ImperialCollegeLondon/Interface-Matters/gumi/base/stl/BaseTop.stl

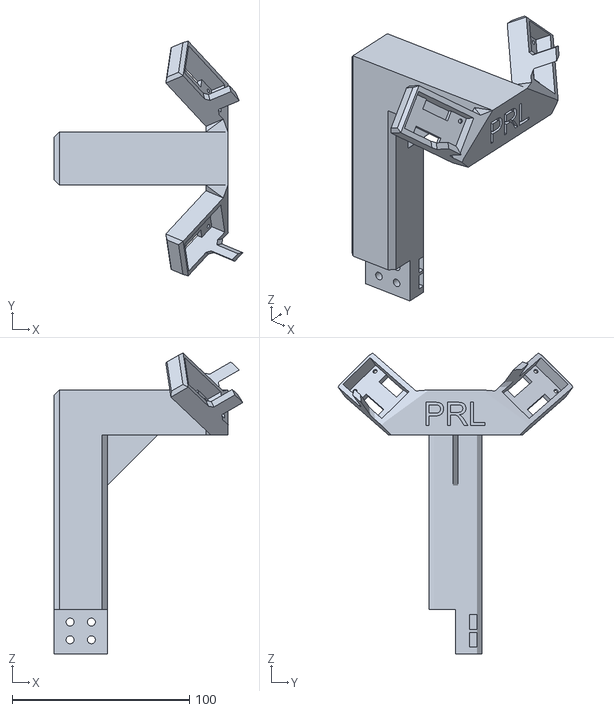
[picture p24: CAD file, 2025-05-07]
gumi/base/stl/BaseTop.stl
106.4 x 132.5 x 169.8
