ImperialCollegeLondon/Interface-Matters/gumi/arm/stl/Link1.stl

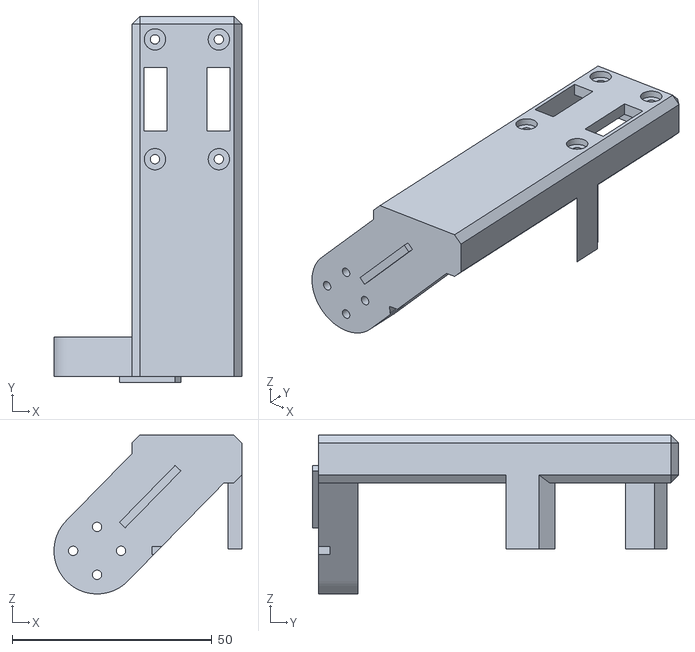
[picture p25: CAD file, 2025-05-07]
gumi/arm/stl/Link1.stl
47.1 x 91.8 x 39.8
